Dimaasd/MultiKey-Rfid-iButton-Read-Write-Emulate/jpg/IMG_20260224_112307.jpg

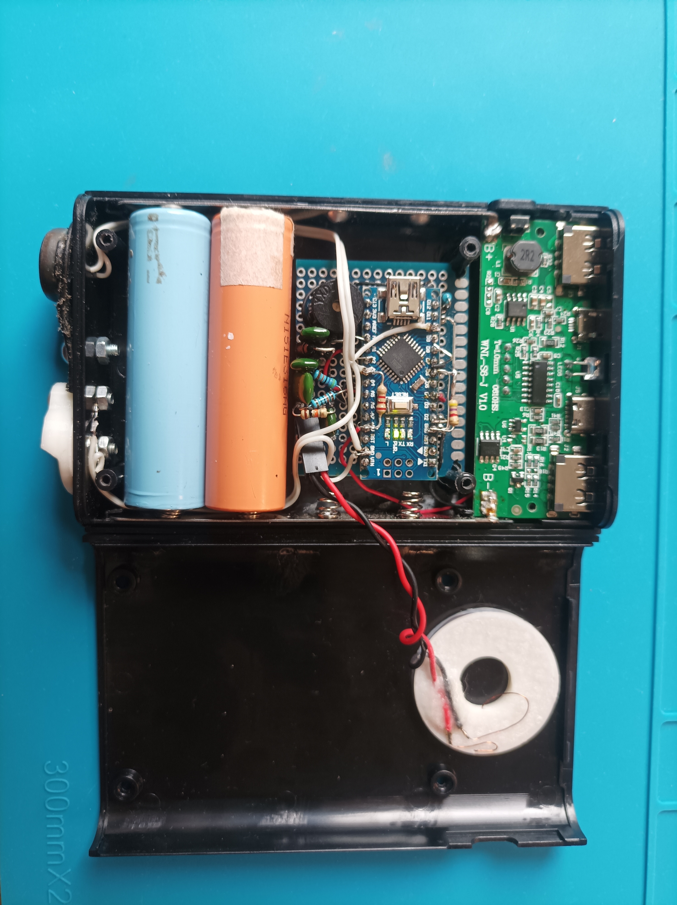
jpg/IMG_20260224_112307.jpg
