Dimaasd/MultiKey-Rfid-iButton-Read-Write-Emulate/jpg/IMG_20260224_112410.jpg

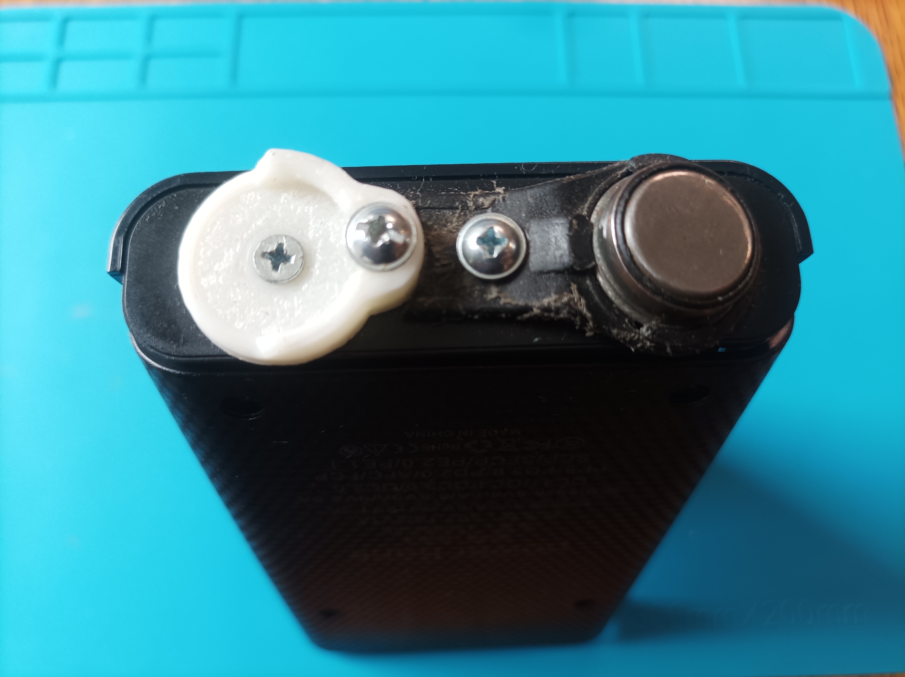
jpg/IMG_20260224_112410.jpg
