Dimaasd/MultiKey-Rfid-iButton-Read-Write-Emulate/jpg/IMG_20260224_112503.jpg

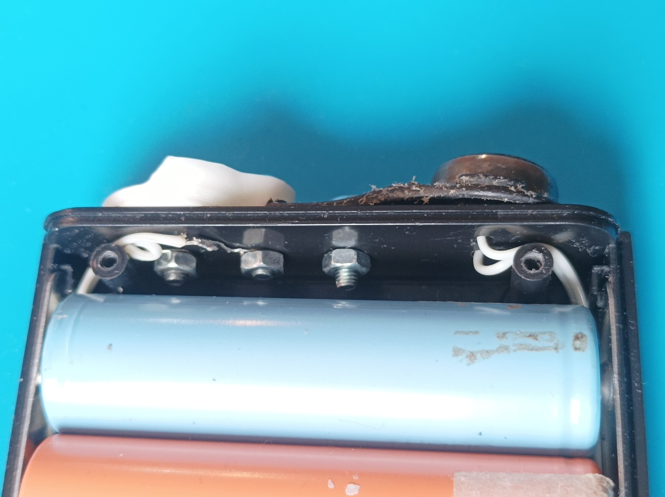
jpg/IMG_20260224_112503.jpg
