Dimaasd/MultiKey-Rfid-iButton-Read-Write-Emulate/jpg/IMG_20260224_112600.jpg

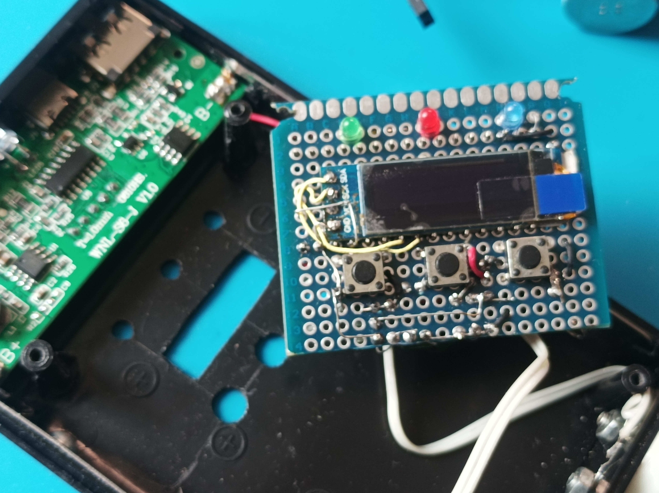
jpg/IMG_20260224_112600.jpg
