Dimaasd/MultiKey-Rfid-iButton-Read-Write-Emulate/jpg/IMG_20260224_114048.jpg

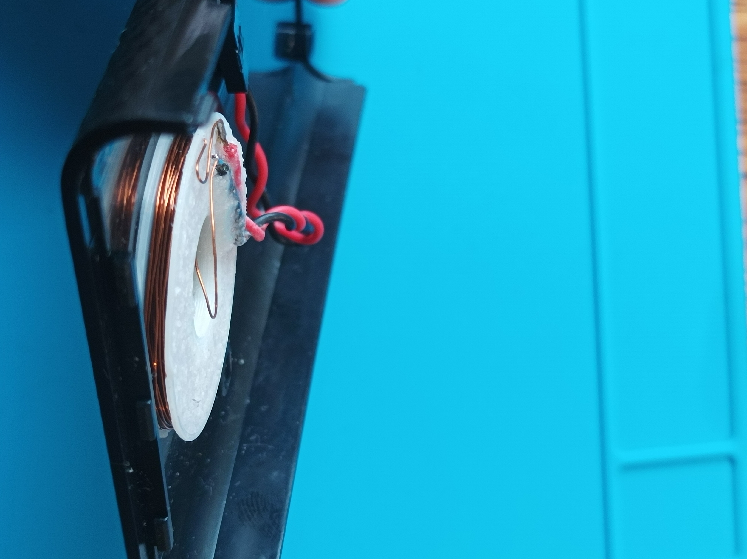
jpg/IMG_20260224_114048.jpg
